angelnu/LorawanSensor/src/sleep.h

#ifndef sleep_h
#define sleep_h

#include "Arduino.h"

const size_t SLEEP_MODE_DEEPSLEEP = 0;
const size_t SLEEP_MODE_DEEPSLEEP_WITH_AC = 1;
const size_t SLEEP_MODE_PRECISE = 2;

void sleep_setup();

void do_sleep(uint32_t sleepTime, size_t mode = SLEEP_MODE_DEEPSLEEP);

void loop_periodically(uint32_t ms, void (&loop_work)());

// Request next sleep to be shorter
// NOTEs:
// - reset back to default sleep time at the begining of loop
// - if several calls are done the smallest one is used
void fast_sleep(uint32_t ms);
bool is_fast_sleep(); //Also return true if it woke up ahead of time (interrupt)
uint32_t next_sleep_time();

//Skip next sleep if more work is needed
void skip_sleep();
bool is_skip_sleep();

#endif
